Dannas2004/Arduino-State-Machine-Arm/3 DOF Robot Circuit.kicad_sch

## KiCad design 3 DOF Robot Circuit.kicad_sch (2026-07-03)

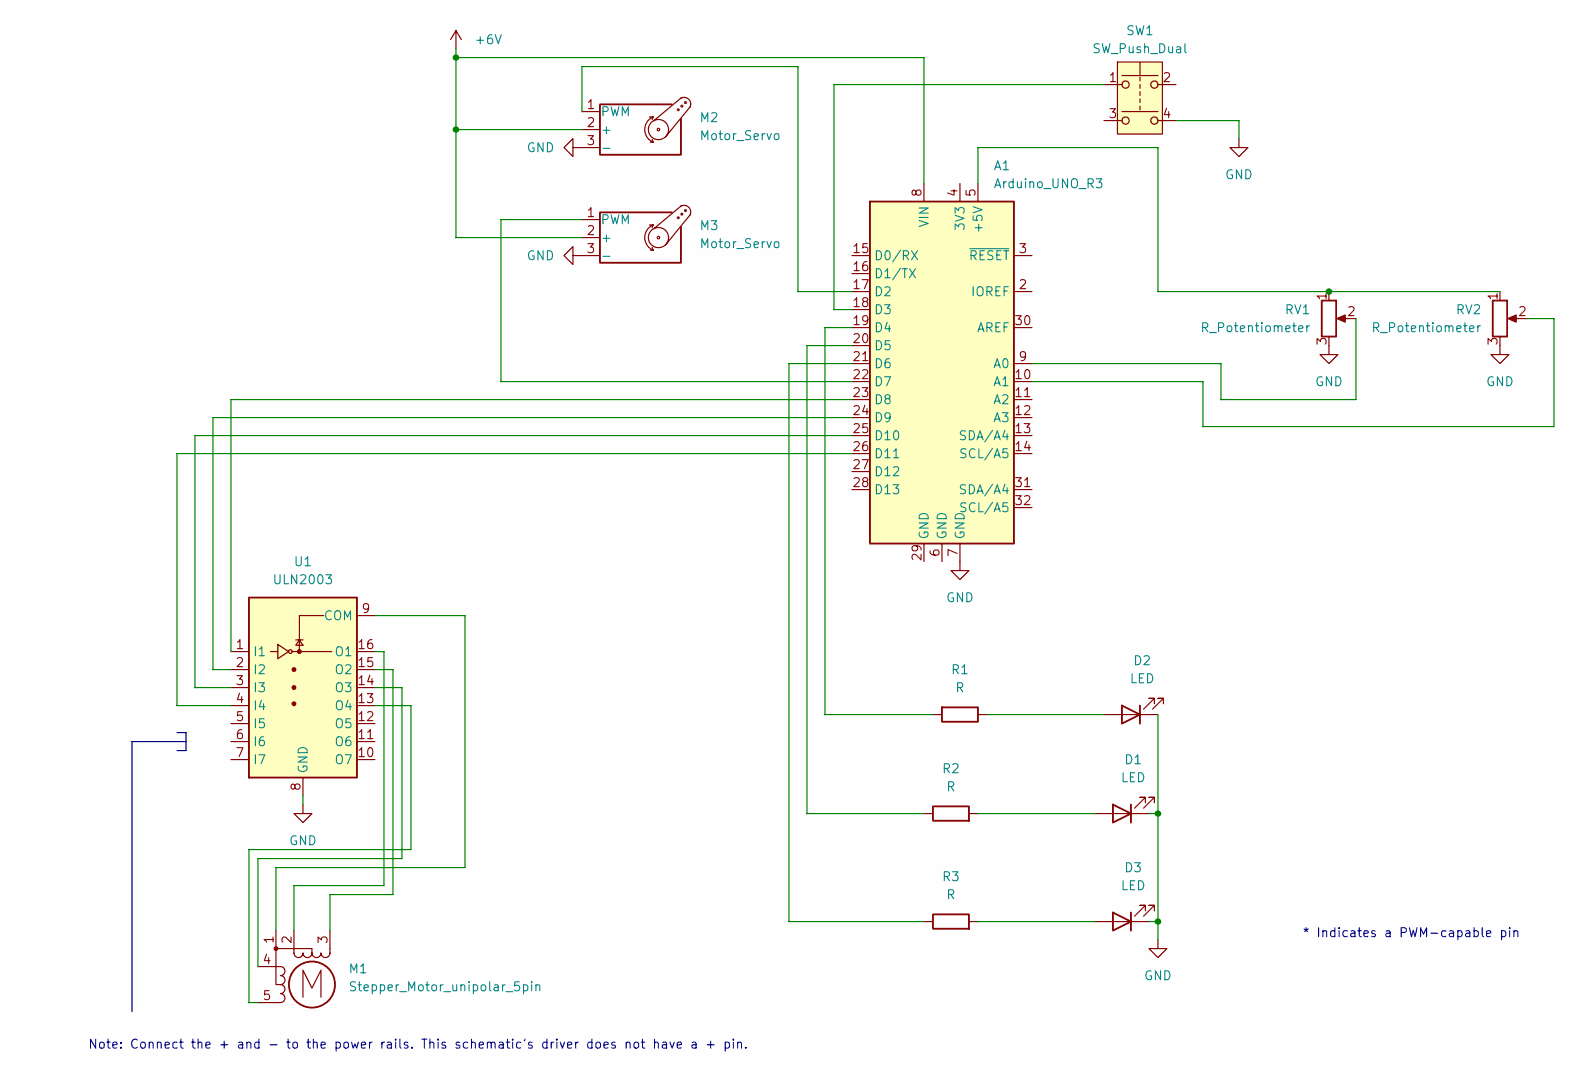
[picture p8: schematic 3 DOF Robot Circuit.kicad_sch]

Parts:
A1: Arduino_UNO_R3
D1, D2, D3: LED
M1: Stepper_Motor_unipolar_5pin
M2, M3: Motor_Servo
R1, R2, R3: R
RV1, RV2: R_Potentiometer
SW1: SW_Push_Dual
U1: ULN2003

Connections:
+6V: A1.8 (VIN), M2.2 (+), M3.2 (+)
GND: A1.7 (GND), D1.1 (K), D2.1 (K), D3.1 (K), M2.3 (-), M3.3 (-), RV1.3, RV2.3, SW1.4, U1.8 (GND)
unnamed: A1.5 (+5V), RV1.1, RV2.1
unnamed: A1.9 (A0), RV1.2
unnamed: A1.10 (A1), RV2.2
unnamed: A1.17 (D2), M2.1 (PWM)
unnamed: A1.18 (D3), SW1.1
unnamed: A1.19 (D4), R1.2
unnamed: A1.20 (D5), R2.1
unnamed: A1.21 (D6), R3.1
unnamed: A1.22 (D7), M3.1 (PWM)
unnamed: A1.23 (D8), U1.1 (I1)
unnamed: A1.24 (D9), U1.2 (I2)
unnamed: A1.25 (D10), U1.3 (I3)
unnamed: A1.26 (D11), U1.4 (I4)
unnamed: D1.2 (A), R2.2
unnamed: D2.2 (A), R1.1
unnamed: D3.2 (A), R3.2
unnamed: M1.1, U1.9 (COM)
unnamed: M1.2, U1.16 (O1)
unnamed: M1.3 (-), U1.15 (O2)
unnamed: M1.4, U1.14 (O3)
unnamed: M1.5, U1.13 (O4)

Notes on the sheet:
Note: Connect the + and - to the power rails. This schematic's driver does not have a + pin.
* Indicates a PWM-capable pin
